Fejiberglibstein/arduino-paint/proximity.cpp

#include "./proximity.h"
#include <assert.h>
#include <math.h>
#include <sys/types.h>
#include <Arduino.h>

#define INTERSECTION_POINTS 12
#define EPSILON 1.3
#define MINIMUM_RADIUS 2
#define MINIMUM_INTERSECTION 2

struct PointCount {
    Point point;
    int count;
};

void add_point_count(
    struct PointCount points[INTERSECTION_POINTS],
    int *point_length,
    Point point
) {
    if (point.x == 0 || point.y == 0) {
        return;
    }
    for (int i = 0; i < *point_length; i++) {
        Point cur = points[i].point;

        // Same point
        if (fabs(cur.x - point.x) <= EPSILON && fabs(cur.y - point.y) <= EPSILON) {
            points[i].count += 1;
            return;
        }
    }

    points[*point_length] = (struct PointCount){.point = point, .count = 1};
    *point_length += 1;
}

Point calculate_point(Circle circles[4]) {
    // We need to get the intersection point(s) between each pair of circles. We
    // can do this by creating an array of pairs of circles and iterating over
    // that to find the most common point where the circles overlap

    /*Serial.println("\n\n\n\n\n");*/
    for (int i = 0; i < 4; i++) {
        /*Serial.println(circles[i].radius);*/
        if (circles[i].radius < MINIMUM_RADIUS) {
            return (Point){
                .x = -1,
                .y = -1,
            };
        }
    }

    // TODO: We probably don't need to do this many checks, we could probably
    // simplify to just adjacent circles?
    //
    // Removing this number of will require `INTERSECTION_POINTS` to be changed
    // as well
    Circle patterns[6][2] = {
        {circles[0], circles[1]},
        {circles[0], circles[2]},
        {circles[0], circles[3]},
        {circles[1], circles[2]},
        {circles[1], circles[3]},
        {circles[2], circles[3]},
    };

    // Array of all possible circle intersection points. We use a count to
    // determine which point is most common; this will be our overall
    // intersection point
    struct PointCount points[INTERSECTION_POINTS] = {0};
    int points_length = 0;

    // Go through all pairs of circles and get the two points of intersection
    // between the circles
    /*Serial.println();*/
    for (int i = 0; i < (sizeof(patterns) / sizeof(*patterns)); i++) {
        Circle *pattern = patterns[i];

        Point p1 = {0};
        Point p2 = {0};
        circle_intersection(pattern[0], pattern[1], &p1, &p2);

        /*Serial.print(p1.x);*/
        /*Serial.print(", ");*/
        /*Serial.print(p1.y);*/
        /*Serial.print("\t\t");*/
        /*Serial.print(p2.x);*/
        /*Serial.print(", ");*/
        /*Serial.println(p2.y);*/


        add_point_count(points, &points_length, p1);
        add_point_count(points, &points_length, p2);
    }

    int best_pointcount = 0;
    bool found = false;

    // Find the most common point
    for (int i = 0; i < (sizeof(points) / sizeof(*points)); i++) {
        /*Serial.print(points[i].count);*/
        /*Serial.print(" ");*/
        if (points[i].count >= points[best_pointcount].count) {
            best_pointcount = i;
            if (points[i].count >= MINIMUM_INTERSECTION) {
                found = true;
            }
        }
    }

    if (!found) {
        return (Point){
            .x = -1,
            .y = -1,
        };
    }
    /*Serial.println("\nFOUND");*/

    return points[best_pointcount].point;
}

int circle_intersection(Circle c1, Circle c2, Point *res1, Point *res2) {
    // https://gist.github.com/jupdike/bfe5eb23d1c395d8a0a1a4ddd94882ac
    // https://math.stackexchange.com/questions/256100/how-can-i-find-the-points-at-which-two-circles-intersect

    assert(c1.radius > 0 && "Radius should be positive");
    assert(c2.radius > 0 && "Radius should be positive");

    float r1 = c1.radius;
    float r2 = c2.radius;

    float x1 = c1.center.x;
    float x2 = c2.center.x;

    float y1 = c1.center.y;
    float y2 = c2.center.y;

    float dx = x1 - x2;
    float dy = y1 - y2;

    float dist = sqrt(dx * dx + dy * dy);

    if (fabs(r1 - r2) > dist || dist > r1 + r2) {
        return 0;
    }

    float dist2 = dist * dist;
    float dist4 = dist2 * dist2;

    float r1_2 = r1 * r1;
    float r2_2 = r2 * r2;

    float a = (r1_2 - r2_2) / (2 * dist2);
    float c = sqrt(2 * (r1_2 + r2_2) / dist2 - ((r1_2 - r2_2) * (r1_2 - r2_2)) / dist4 - 1);

    float fx = (x1 + x2) / 2 + a * (x2 - x1);
    float gx = c * (y2 - y1) / 2;

    float fy = (y1 + y2) / 2 + a * (y2 - y1);
    float gy = c * (x1 - x2) / 2;

    *res1 = (Point){.x = fx + gx, .y = fy + gy};
    *res2 = (Point){.x = fx - gx, .y = fy - gy};

    return 2;
}

int ggf() {
    return 0;
}
