Fejiberglibstein/arduino-paint/math_lib/proximity.h

#ifndef PROXIMITY_H
#define PROXIMITY_H

typedef struct {
    float x;
    float y;
} Point;

typedef struct {
    float radius;
    Point center;
} Circle;

/// Calculate the point that is at the intersection of all 4 circles.
Point calculate_point(Circle[4]);

/// Get the intersection point(s) between two circles.
///
/// Will return 0 if the circles intersect, 1 if there is one point of
/// intersection, and 2 if there are 2 points of intersection.
///
/// The computed points will be set to the passed in `Point_t` pointers.
int circle_intersection(Circle, Circle, Point *, Point *);

#endif
