Fejiberglibstein/arduino-paint/tests/ultrasonic_sensors.ino/ultrasonic_sensors.ino.ino

// defines pins numbers
const int trigPin = 4;
const int echoPin = 4;
// defines variables
long duration;
int distance;

// Use this to find angle and range of the individual sensor
// We got ~ 50 degrees
void setup() {
  // pinMode(trigPin, OUTPUT); // Sets the trigPin as an Output
  // pinMode(echoPin, INPUT); // Sets the echoPin as an Input
  Serial.begin(115200); // Starts the serial communication
}

void loop() {
  // Clears the trigPin
  pinMode(trigPin, OUTPUT);
  digitalWrite(trigPin, LOW);
  delayMicroseconds(2);
  // Sets the trigPin on HIGH state for 10 micro seconds
  digitalWrite(trigPin, HIGH);
  delayMicroseconds(10);
  digitalWrite(trigPin, LOW);
  pinMode(echoPin, INPUT);
  // Reads the echoPin, returns the sound wave travel time in microseconds
  duration = pulseIn(echoPin, HIGH);
  // Calculating the distance
  distance = duration * 0.0343 / 2;
  // Prints the distance on the Serial Monitor
  Serial.print("Distance: ");
  Serial.println(distance);
}
